bnahill/wireless_logger/sw_imu/src/platform/sf/platform.cpp

/*!
 @file platform.cpp
 
 @brief Platform-specific instantiations
 
 @author Ben Nahill <bnahill@gmail.com>
 */
#define __PLATFORM_CPP_

#include "platform.h"
#include "platform_usbserial.h"
#include "flogfs.h"

#include "imu/ssd1306.cpp"
#include "imu/datasource.cpp"
#include "imu/mma845x.cpp"
#include "imu/clock_mgr.h"


using namespace Platform;

template <GPIO_TypeDef * gpio_temp,
          uint32_t mask,
          uint32_t direction,
          uint32_t pull,
          uint32_t af>
class pin_t {
	static constexpr GPIO_TypeDef * gpio = gpio_temp;
};


I2C Platform::i2c1(I2CD1, OPMODE_I2C, FAST_DUTY_CYCLE_2, 400000, {GPIOB, 9}, {GPIOB, 8});
//I2C Platform::i2c2(I2CD2, OPMODE_I2C, FAST_DUTY_CYCLE_2, 400000, {GPIOH, 5}, {GPIOH, 4});
//I2C Platform::i2c3(I2CD3, OPMODE_I2C, FAST_DUTY_CYCLE_2, 400000, {GPIOC, 9}, {GPIOA, 8});
template class MMA845x<MMA8451Q_T>;
MMA8451Q Platform::acc1(Platform::i2c1, 0x1C);
MAG3110 Platform::mag1(Platform::i2c1, 0x0E);
LPS331 Platform::prs1(Platform::spi3, {NULL, GPIOD, 5, SPI_CR1_BR_2 |
                                       SPI_CR1_BR_1 | SPI_CR1_CPOL |
                                       SPI_CR1_CPHA});


template class DataSource<Euclidean3_f32>;
template class DataListener<Euclidean3_f32>;
DataSource<Euclidean3_f32> Platform::acc_source;
DataSource<Euclidean3_f32> Platform::mag_source;
DataSource<Euclidean3_f32> Platform::gyro_source;

template class DataSource<float>;
template class DataListener<float>;
DataSource<float> Platform::prs_source;

///////////////////////////////////////////
// SPI Platform
///////////////////////////////////////////

SPI Platform::spi1(SPID1);
SPI Platform::spi2(SPID2);
SPI Platform::spi3(SPID3);

///////////////////////////////////////////
// L3GD20 Platform
///////////////////////////////////////////

L3GD20_SPI Platform::gyro1(Platform::spi3, {NULL, GPIOB, 5, SPI_CR1_BR_2 |
                                            SPI_CR1_BR_1 | SPI_CR1_CPOL |
                                            SPI_CR1_CPHA});


///////////////////////////////////////////
// Button platform configuration
///////////////////////////////////////////

button_t Platform::button[4] = {
	{GPIOD, 7, button_t::ACTIVE_LOW},
	{GPIOF, 6, button_t::ACTIVE_LOW},
	{GPIOC, 5, button_t::ACTIVE_LOW},
	{GPIOE, 8, button_t::ACTIVE_LOW}
};

///////////////////////////////////////////
// Edge-trigger interrupt configuration
///////////////////////////////////////////

const EXTConfig Platform::extcfg = {
	{
		{EXT_CH_MODE_DISABLED, NULL}, // 0
		{EXT_CH_MODE_DISABLED, NULL},
		{EXT_CH_MODE_DISABLED, NULL},
		{EXT_CH_MODE_DISABLED, NULL},
		{EXT_CH_MODE_DISABLED, NULL},
		{EXT_CH_MODE_BOTH_EDGES | EXT_CH_MODE_AUTOSTART | EXT_MODE_GPIOC,
			Ext1Callback::callback}, // 5
		{EXT_CH_MODE_BOTH_EDGES | EXT_CH_MODE_AUTOSTART | EXT_MODE_GPIOF,
			Ext1Callback::callback},
		{EXT_CH_MODE_BOTH_EDGES | EXT_CH_MODE_AUTOSTART | EXT_MODE_GPIOD,
			Ext1Callback::callback},
		{EXT_CH_MODE_BOTH_EDGES | EXT_CH_MODE_AUTOSTART | EXT_MODE_GPIOE,
			Ext1Callback::callback},
		{EXT_CH_MODE_DISABLED, NULL},
		{EXT_CH_MODE_DISABLED, NULL}, // 10
		{EXT_CH_MODE_DISABLED, NULL},
		{EXT_CH_MODE_DISABLED, NULL},
		{EXT_CH_MODE_DISABLED, NULL},
		{EXT_CH_MODE_DISABLED, NULL},
		{EXT_CH_MODE_DISABLED, NULL}, // 15
		{EXT_CH_MODE_DISABLED, NULL},
		{EXT_CH_MODE_DISABLED, NULL},
		{EXT_CH_MODE_DISABLED, NULL},
		{EXT_CH_MODE_DISABLED, NULL},
		{EXT_CH_MODE_DISABLED, NULL}, // 20
		{EXT_CH_MODE_DISABLED, NULL},
		{EXT_CH_MODE_DISABLED, NULL}
	}
};

///////////////////////////////////////////
// LED platform configuration
///////////////////////////////////////////

gpio_pin_t Platform::led1(GPIOE, 5);
gpio_pin_t Platform::led2(GPIOE, 3);
gpio_pin_t Platform::led3(GPIOE, 2);


//LTC3559 Platform::reg1({GPIOC, 2}, {GPIOC, 1}, {GPIOA, 4}, {GPIOA, 1});

///////////////////////////////////////////
// OLED display platform configuration
///////////////////////////////////////////


template class SSD1306<4,128>;
template class FrameBuffer<4, 128>;


LY091WG15 Platform::oled(spi1,
                        {NULL, GPIOF, 10, SPI_CR1_BR_0 |
                         SPI_CR1_CPOL | SPI_CR1_CPHA},
                        {GPIOA, 3}, {GPIOH, 2});

usbserial1_t Platform::usbserial1({GPIOA, 9});


///////////////////////////////////////////
// CC1101 platform configuration
///////////////////////////////////////////

// CC1101 Platform::rf1(Platform::spi1,
//                      {NULL, GPIOC, 9, SPI_CR1_BR_2 | SPI_CR1_BR_1});

CC1101 Platform::rf1(Platform::spi2,
                     {NULL, GPIOE, 15, SPI_CR1_BR_2 | SPI_CR1_BR_1});

GuardianRF Platform::guardian1(rf1);

//////////////////////////////////////////////////////////
// Flash platform configuration
//////////////////////////////////////////////////////////

MT29FxG01 Platform::flash(spi1, MT29FxG01::SIZE_1G,
                         {GPIOD, 6},(SPI_CR1_CPOL | SPI_CR1_CPHA));



//////////////////////////////////////////////////////////
// Platform initialization
//////////////////////////////////////////////////////////

EventLog Platform::evt_log;

void Platform::early_init(){
	clk_mgr_init();
	
// 	reg1.high_power(true);
// 	reg1.buck_mode(LTC3559::MODE_BURST);
	rf1.early_init();


	evt_log.init();


	if(flogfs_init() != FLOG_SUCCESS){
		evt_log.add("FLogFS init\n failed!", EventItem::SEVERITY_ERROR);
	} else {
		if(flogfs_mount() != FLOG_SUCCESS){
			evt_log.add("FLogFS mount\n failed!", EventItem::SEVERITY_ERROR);
		}
	}

	
	extStart(&EXTD1, &extcfg);
}


// Lockable * const Platform::buses[] = {
// 	&i2c1,
// 	&spi1,
// 	&spi2,
// 	nullptr
// };

extern "C" {
void NMIVector(void){while(1);}
void HardFaultVector(void){
	asm volatile ("MRS R0,PSP");
	asm volatile ("LDR R1,[R0,#24]");

	while(1);
}
void MemManageVector(void){while(1);}
void BusFaultVector(void){while(1);}
void UsageFaultVector(void){while(1);}
}
