bnahill/wireless_logger/sw_imu/imu/usbserial.h

/*!
 @file usbserial.h
 @brief Declaration for \ref USBSerial driver
 @author Ben Nahill <bnahill@gmail.com>
 */

#ifndef __IMU_USB_SERIAL_H_
#define __IMU_USB_SERIAL_H_

#include "ch.h"
#include "hal.h"
#include "serial_usb.h"
#include "chprintf.h"
#include "imu.h"

//! @addtogroup IMU
//! @{
//! @addtogroup USBSerial
//! @{


/*!
 @brief An abstracted USB CDC device driver
 @tparam usb_driver The ChibiOS USB driver object to use
 
 @note Some of components are declared as generic templated functions but
 some (descriptor info) has to be specialized in the platform
 */
template <USBDriver &usb_driver>
class USBSerial {
public:
	USBSerial< usb_driver >(gpio_pin_t const &vusb_pin) :
		vusb_pin(vusb_pin)
	{
		sduObjectInit(&driver);
	}
	
	/*!
	 @brief Initialize the hardware
	 */
	void init(){
		clk_mgr_req_hse();
		
		//usbDisconnectBus(conf.usbp);
		//chThdSleepMilliseconds(1000);
		//usbStart(conf.usbp, &usbcfg);
		sduObjectInit(&driver);
		sduStart(&driver, &conf);
		
		usbDisconnectBus(conf.usbp);
		chThdSleepMilliseconds(1000);
		usbStart(conf.usbp, &usbcfg);
	    usbConnectBus(conf.usbp);
	}
	
	void stop(){
		usbStop(conf.usbp);
		sduStop(&driver);
		clk_mgr_noreq_hse();
	}
	
	bool is_connected() const { return vusb_pin.read(); }
	
	BaseSequentialStream * stream()  {
		return reinterpret_cast<BaseSequentialStream *>(&driver);
	}
	
	SerialUSBDriverVMT const * vmt() const {
		return driver.vmt;
	}
	
	void write_byte(uint8_t byte){
		chSequentialStreamPut(stream(), byte);
	}
	
	void write_buffer(uint8_t const * buf, uint32_t len){
		chSequentialStreamWrite(&driver, buf, len);
	}
	
	size_t read(uint8_t *bp, size_t n, systime_t time){
		return chIQReadTimeout(&driver.iqueue, bp, n, time);
	}

protected:
	//! @name Implemtented in driver
	//! @{	
	SerialUSBDriver driver;
	gpio_pin_t const vusb_pin;
	
	USBInEndpointState ep1instate;
	USBOutEndpointState ep1outstate;
	USBInEndpointState ep2instate;
	USBOutEndpointState ep2outstate;
	//! @}
	
	//! @name Implemtented in driver
	//! @{

	static USBDescriptor const * get_descriptor(USBDriver *usbp,
	                                            uint8_t dtype,
	                                            uint8_t dindex,
	                                            uint16_t lang);
	
	static const SerialUSBConfig conf;	
	
	static const USBEndpointConfig ep1config;
	static const USBEndpointConfig ep2config;
	
	static const USBDescriptor vcom_strings[];
	
	static const USBConfig usbcfg;
	
	static void usb_event(USBDriver *usbp, usbevent_t event);
	//! @}
	
	//! @name To implement as template specialization
	//! @{

	//! A reference to this device accessible from static context
	static USBSerial &this_device;
	
	static const uint8_t vcom_device_descriptor_data[18];
	static const USBDescriptor vcom_device_descriptor;
	static const uint8_t vcom_configuration_descriptor_data[];
	static const uint8_t vcom_string0[];
	static const uint8_t vcom_string1[];
	static const uint8_t vcom_string2[];
	static const uint8_t vcom_string3[];
	static const USBDescriptor vcom_configuration_descriptor;
	//! @}
};

#include "imu/usbserial.cpp"

//! @} @}

#endif // __IMU_USB_SERIAL_H_
