bnahill/wireless_logger/sw_imu/imu/spi.h

/*!
 @file spi.h
 @brief Declaration for \ref SPI driver
 @author Ben Nahill <bnahill@gmail.com>
 */

#ifndef __IMU_SPI_H_
#define __IMU_SPI_H_

#include "ch.h"
#include "hal.h"
#include "imu/imu.h"

//! @addtogroup IMU
//! @{
//! @addtogroup SPI
//! @{

//class SPI : public LockableSem {
/*!
 @brief A 4-wire SPI driver
 */
class SPI {
public:
	/*
	typedef struct {
		gpio_pin_t nss;
		uint32_t max_freq;
		uint32_t cr1_flags;
	} slave_config_t;
	*/
	
	typedef SPIConfig slave_config_t;
	
	
	typedef enum {
		OP_READ,     //!< A single-word write followed by an arbitrary length
		             //!< read
		OP_WRITE,    //!< A single-word write followed by an arbitrary length
		             //!< write
		OP_EXCHANGE, //!< A simple exchange of two buffers
		OP_SEND,     //!< Just transmit an arbitrary number of bytes
		OP_WR_SEQ,   //!< Write an arbitrary amount of data, then read an
		             //!< arbitrary amount of data
		OP_WW_SEQ,   //!< Write an arbitrary amount of data, then write
		             //!< another arbitrary amount of data
	} operation_t;
	
	typedef void (*callback)(void *);


	struct xfer_t {
		//! Constructor for synchronous exchange
		xfer_t(slave_config_t const * config, size_t n,
		       void const * tx_buff, void * rx_buff) :
			config(config), n_tx(n),
			tc_callback(nullptr), starting_callback(nullptr),
			operation(OP_EXCHANGE), rx_buff(rx_buff), tx_buff(tx_buff)
		{}
		
		//! Constructor for send
		xfer_t(slave_config_t const * config, size_t n, void const * tx_buff) :
			config(config), n_tx(n),
			tc_callback(nullptr), starting_callback(nullptr),
			operation(OP_SEND), tx_buff(tx_buff)
		{}
		
		//! A more generic constructor
		xfer_t(slave_config_t const * config, size_t n, operation_t op) :
			config(config), n_tx(n), operation(op),
			tc_callback(nullptr), starting_callback(nullptr)
		{}

		//! Slave information
		slave_config_t const * config;
		//! @name Callbacks
		//! @brief Set to 0 to not use
		//! @{
		//! Callback for when the transfer is completely done
		callback tc_callback;
		//! Callback for when the transfer is just about to start
		callback starting_callback;
		void *tc_param;
		void *starting_param;
		//! @}
		//! @name Transfer details
		//! @{
		//! The operation to perform
		operation_t operation;
		//! Number of bytes to send or exchange
		size_t n_tx;
		//! Number of bytes to receive (if not exchanging)
		size_t n_rx;
		//! Buffer to write
		void const * tx_buff;
		//! Buffer to store received information
		void * rx_buff;
		//! Address for read or write transfers
		uint16_t addr;
		//! @}
	};
	
	struct new_xfer_t {
		enum {
			XOP_EXCHANGE, //!< A simple exchange of two buffers
			XOP_SEND,     //!< Just transmit an arbitrary number of bytes
			XOP_RECV,     //!< Just receive an arbitrary number of bytes
		} op;
		uint8_t * rx_buff;
		uint8_t const * tx_buff;
		uint32_t n;
		union {
			uint32_t word;
			uint8_t bytes[4];
		};
	};
	
	struct message_t {
		uint32_t num_xfers;
		new_xfer_t * xfer;
		callback tc_callback;
		void *tc_param;
	};
	
	SPI(SPIDriver &driver);
	
	void init();
	
	/*!
	 @brief Add a transfer to the transfer queue
	 @param xfer The transfer to add
	 @param important Push to front of queue?
	 */
	void transfer(xfer_t &xfer, bool important=false);
	
	
	void reconfig_clock();
	
	/*!
	 @brief Perform a synchronous exchange with a peripheral
	 @param config The slave configuration to use
	 @param n The number of bytes to exchange
	 @param tx_buff The n-length buffer to transmit
	 @param rx_buff The n-length receive buffer
	 @param important Force to front of queue?
	 */
	void exchange_sync(slave_config_t const &config, size_t n,
	                   void const * tx_buff, void * rx_buff,
	                   bool important=false);
	
	/*!
	 @brief Perform a synchronous transmission
	 @param config The slave configuration to use
	 @param n The number of bytes to send
	 @param tx_buff The n-length buffer to transmit
	 @param important Force to front of queue?
	 */
	void send_sync(slave_config_t const &config, size_t n,
	               void const * tx_buff, bool important=false);
	
	/*!
	 @brief Perform a synchronous transmission
	 @param config The slave configuration to use
	 @param addr The address to write to
	 @param n The number of bytes to send
	 @param tx_buff The n-length buffer to transmit
	 @param important Force to front of queue?
	 @return The value read during address transmission
	 */
	uint16_t write_sync(slave_config_t const &config, uint16_t addr, size_t n,
	                void const * tx_buff, bool important=false);
	
	/*!
	 @brief Perform a synchronous receive operation
	 @param config The slave configuration to use
	 @param addr The address to write to
	 @param n The number of bytes to send
	 @param rx_buff The n-length buffer to receive to
	 @param important Force to front of queue?
	 @return The value read during address transmission
	 */
	uint16_t read_sync(slave_config_t const &config, uint16_t addr, size_t n,
	                void * rx_buff, bool important=false);
	
	void wr_sequence_sync(slave_config_t const &config, uint8_t const * tx,
	                      uint16_t n_tx, uint8_t * rx, uint16_t n_rx,
	                      bool important = false);
	
	void ww_sequence_sync(slave_config_t const &config, uint8_t const * tx0,
	                      uint16_t n_tx0, uint8_t const * tx1, uint16_t n_tx1,
	                      bool important = false);
	
	void lock(){
		spiAcquireBus(&driver);
	}
	
	void unlock(){
		spiReleaseBus(&driver);
	}
	
protected:
	//! The ChibiOS SPI resource
	SPIDriver &driver;
	
	/*!
	 @brief Flag to indicate that it shouldn't be re-initialized.
	 @note This variable should be accessed only under lock.
	 */
	bool is_init;
	
	bool do_sleep;
};


//! @} @}

#endif // __IMU_SPI_H_
