bnahill/wireless_logger/sw_imu/src/platform/flogfs_conf_implement.h

/*
Copyright (c) 2013, Ben Nahill <bnahill@gmail.com>
All rights reserved.

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
1. Redistributions of source code must retain the above copyright notice, this
   list of conditions and the following disclaimer.
2. Redistributions in binary form must reproduce the above copyright notice,
   this list of conditions and the following disclaimer in the documentation
   and/or other materials provided with the distribution.

THIS SOFTWARE IS PROVIDED BY THE COPYRIGHT HOLDERS AND CONTRIBUTORS "AS IS" AND
ANY EXPRESS OR IMPLIED WARRANTIES, INCLUDING, BUT NOT LIMITED TO, THE IMPLIED
WARRANTIES OF MERCHANTABILITY AND FITNESS FOR A PARTICULAR PURPOSE ARE
DISCLAIMED. IN NO EVENT SHALL THE COPYRIGHT OWNER OR CONTRIBUTORS BE LIABLE FOR
ANY DIRECT, INDIRECT, INCIDENTAL, SPECIAL, EXEMPLARY, OR CONSEQUENTIAL DAMAGES
(INCLUDING, BUT NOT LIMITED TO, PROCUREMENT OF SUBSTITUTE GOODS OR SERVICES;
LOSS OF USE, DATA, OR PROFITS; OR BUSINESS INTERRUPTION) HOWEVER CAUSED AND
ON ANY THEORY OF LIABILITY, WHETHER IN CONTRACT, STRICT LIABILITY, OR TORT
(INCLUDING NEGLIGENCE OR OTHERWISE) ARISING IN ANY WAY OUT OF THE USE OF THIS
SOFTWARE, EVEN IF ADVISED OF THE POSSIBILITY OF SUCH DAMAGE.

The views and conclusions contained in the software and documentation are those
of the authors and should not be interpreted as representing official policies,
either expressed or implied, of the FLogFS Project.
*/

/*!
 * @file flogfs_conf.cpp
 * @author Ben Nahill <bnahill@gmail.com>
 * @ingroup FLogFS
 *
 * @brief Platform-specific interface details
 */

#include "flogfs.h"

#include "platform.h"

using namespace Platform;

typedef uint8_t flash_spare_t[59];

typedef Mutex fs_lock_t;


static inline void fs_lock_init(fs_lock_t * lock){
	chMtxInit(lock);
}

static inline void fs_lock(fs_lock_t * lock){
	chMtxLock(lock);
}

static inline void fs_unlock(fs_lock_t * lock){
	chMtxUnlock();
}

static flash_spare_t flog_spare_buffer;
static uint8_t page_open;

static inline flog_result_t flash_init(){
	return FLOG_RESULT(flash.init());
}

static inline void flash_lock(){
	flash.lock();
}

static inline void flash_unlock(){
	flash.unlock();
}

static inline flog_result_t flash_open_page(uint16_t block, uint16_t page){
	// Read flash page to cache
	return FLOG_RESULT(flash.page_open(block, page));
}

static inline flog_result_t flash_open_page_write(uint16_t block, uint16_t page){
	// Read flash page to cache
	return FLOG_RESULT(flash.page_open_write(block, page));
}

static inline flog_result_t flash_erase_block(uint16_t block){
	return FLOG_RESULT(flash.erase_block(block));
}


static inline uint8_t * flash_spare(uint8_t sector){
	return &flog_spare_buffer[sector * 16 + 4];
}

static inline flog_result_t flash_block_is_bad(){
	uint8_t buffer;
	flash.page_read_continued(&buffer, 0x800, 1);
	return FLOG_RESULT(buffer != 0xFF);
}

static inline void flash_set_bad_block(){

}

/*!
 @brief Commit the changes to the active page
 */
static inline void flash_commit(){
	page_open = 0;
	flash.page_commit();
}

/*!
 @brief Read data from the flash cache (current page only)
 @param dst The destination buffer to fill
 @param chunk_in_page The chunk index within the current page
 @param offset The offset data to retrieve
 @param n The number of bytes to transfer
 @return The success or failure of the operation
 */
static inline flog_result_t flash_read_sector(uint8_t * dst, uint8_t sector, uint16_t offset, uint16_t n){
	sector = sector % FS_SECTORS_PER_PAGE;
	return FLOG_RESULT(flash.page_read_continued(dst, FS_SECTOR_SIZE * sector + offset, n));
}

static inline flog_result_t flash_read_spare(uint8_t * dst, uint8_t sector){
	sector = sector % FS_SECTORS_PER_PAGE;
	return FLOG_RESULT(
	   flash.page_read_continued(dst, 0x804 + sector * 0x10, 4)
	);
}

/*!
 @brief Write chunk data to the flash cache
 @param src A pointer to the data to transfer
 @param chunk_in_page The chunk index within the current page
 @param offset The offset to write the data
 @param n The number of bytes to write
 */
static inline void flash_write_sector(uint8_t const * src, uint8_t sector, uint16_t offset, uint16_t n){
	sector = sector % FS_SECTORS_PER_PAGE;
	flash.page_write_continued(src, FS_SECTOR_SIZE * sector + offset, n);
}


/*!
 @brief Write the spare data for a sector
 @param chunk_in_page The chunk index within the current page

 @note This doesn't commit the transaction
 */
static inline void flash_write_spare(uint8_t const * src, uint8_t sector){
	sector = sector % FS_SECTORS_PER_PAGE;
	flash.page_write_continued(src, 0x804 + sector * 0x10, 4);
}

static inline void flash_debug_warn(char const * msg){
	evt_log.add(msg, EventItem::SEVERITY_WARNING);
}

static inline void flash_debug_error(char const * msg){
	evt_log.add(msg, EventItem::SEVERITY_ERROR);
}
