bnahill/wireless_logger/sw_imu/imu/framebuffer.cpp

/*!
 @file framebuffer.cpp
 
 @brief Templated body for \ref FrameBuffer class
 
 @note This file is not compiled directly; It should be included by your
 platform.
 
 @author Ben Nahill <bnahill@gmail.com>
 */

#include "imu/framebuffer.h"

//! @addtogroup IMU
//! @{
//! @addtogroup FrameBuffer
//! @{

template <uint32_t pages, uint32_t columns>
FrameBuffer< pages, columns >::FrameBuffer(){
	limits.x_min = columns - 1;
	limits.y_min = pages - 1;
	limits.x_max = 0;
	limits.y_max = 0;
	chMtxInit(&mutex);
}

template <uint32_t pages, uint32_t columns>
void FrameBuffer< pages, columns >::clear_area(
	  uint32_t start_page, uint32_t end_page,
	  uint32_t start_column, uint32_t end_column){
	uint32_t i, j;
	lock();
	for(i = start_page; i <= end_page; i++){
		for(j = start_column; j <= end_column; j++){
			fb[i][j] = 0;
		}
	}
	limits.y_min = min(start_page, limits.y_min);
	limits.y_max = max(end_page, limits.y_max);
	limits.x_min = start_column;
	limits.x_max = end_column;
	
	unlock();
}

template <uint32_t pages, uint32_t columns>
void FrameBuffer< pages, columns >::clear(){
	clear_area();
}


template <uint32_t pages, uint32_t columns>
uint32_t FrameBuffer< pages, columns >::write_text_generic(
      write_text_func_t f, char const * text, uint8_t page,
	  uint8_t column, uint32_t max_end_column){
	uint32_t i = 0;
	uint32_t n_cols = 0;
	
	if(*text == 0)
		return n_cols;
	
	lock();
	
	limits.y_min = min(page, limits.y_min);
	limits.x_min = min(column, limits.x_min);
	while(page < pages){
		// Take take the i-th row of the printed text
		if(!f(fb[page] + column, i, text, n_cols,
			                       max_end_column - column)){
			limits.x_max = max(min(n_cols + column, columns), limits.x_max);
			limits.y_max = max(min(page, pages), limits.y_max);
			break;
		}
		
		page += 1;
		i += 1;
	} if (pages == page){
		limits.y_max = pages;
		limits.x_max = max(min(n_cols + column, columns), limits.x_max);
	}
	
	unlock();
	
	return n_cols + column;
}

template <uint32_t pages, uint32_t columns>
void FrameBuffer< pages, columns >::draw_horizontal_mask(uint8_t page,
	  uint8_t mask, uint32_t col_start, uint32_t length){
	uint8_t * iter = &fb[page][col_start];
	lock();
	
	limits.x_min = min(limits.x_min, col_start);
	limits.x_max = max(limits.x_max, col_start + length);
	limits.y_min = min(limits.y_min, page);
	limits.y_max = max(limits.y_max, page);
	while(length--){
		*(iter++) |= mask;
	}
	
	unlock();
}
template <uint32_t pages, uint32_t columns>
void FrameBuffer< pages, columns >::draw_vertical(uint8_t start_page,
	  uint8_t end_page, uint32_t column){
	lock();
	limits.x_min = min(limits.x_min, column);
	limits.x_max = max(limits.x_max, column);
	limits.y_min = min(limits.y_min, start_page);
	limits.x_max = max(limits.y_max, end_page);
	while(start_page != end_page + 1){
		fb[start_page++][column] = 0xFF;
	}
	unlock();
}

template <uint32_t pages, uint32_t columns>
void FrameBuffer< pages, columns >::draw_progress_bar(float value,
	 uint8_t page, uint32_t start_column, uint32_t end_column){

	uint8_t iter;
	uint32_t progress;
	
	value = clamp(value, 0.0f, 1.0f);
	
	progress = value * (end_column - start_column) + 0.5; 
	
	lock();
	limits.x_min = min(limits.x_min, start_column);
	limits.x_max = max(limits.x_max, end_column);
	limits.y_min = min(limits.y_min, page);
	limits.x_max = max(limits.y_max, page);
	
	fb[page][start_column] = 0xFF;
	fb[page][end_column] = 0xFF;
	
	fb[page][start_column + 1] = 0x81;
	for(iter = start_column + 2; iter < progress; iter++){
		fb[page][iter] = 0b10111101; // 0xAD
	}
	for(iter = progress; iter < end_column - 2; iter++){
		fb[page][iter] = 0b10000001; // 0x81
	}
	
	unlock();
}

template <uint32_t pages, uint32_t columns>
void FrameBuffer< pages, columns >::draw_pos_neg_bar(float value,
	  uint8_t page, uint32_t start_column, uint32_t end_column){
	uint8_t iter;
	uint32_t progress;
	uint32_t length = end_column - start_column - 4;
	uint32_t zero_column = start_column + 2 + length / 2;
	
	value = clamp(value, -1.0f, 1.0f);
	
	progress = (int32_t)(0.5f * value * length + 0.5) + zero_column;
	
	lock();
	limits.x_min = min(limits.x_min, start_column);
	limits.x_max = max(limits.x_max, end_column);
	limits.y_min = min(limits.y_min, page);
	limits.x_max = max(limits.y_max, page);
	
	fb[page][start_column] = 0xFF;
	fb[page][end_column] = 0xFF;
	
	// Check if progress bar is to left of zero	
	if(progress < zero_column){
		for(iter = start_column + 1; iter < progress; iter++){
			fb[page][iter] = 0b10000001; // 0x81
		}
		for(iter = progress; iter <= zero_column; iter++){
			fb[page][iter] = 0b10111101; // 0xAD
		}
		for(iter = zero_column + 1; iter < end_column; iter++){
			fb[page][iter] = 0b10000001; // 0x81
		}
	} else {
		for(iter = start_column + 1; iter < zero_column; iter++){
			fb[page][iter] = 0b10000001; // 0x81
		}
		for(iter = zero_column; iter <= progress; iter++){
			fb[page][iter] = 0b10111101; // 0xAD
		}
		for(iter = progress + 1; iter < end_column; iter++){
			fb[page][iter] = 0b10000001; // 0x81
		}
	}
	
	unlock();
}

/*!
	@brief Reset bounds of area to update
	*/
template <uint32_t pages, uint32_t columns>
void FrameBuffer< pages, columns >::sync(bool do_lock){
	if(do_lock)
		lock();
	
	limits.x_min = columns - 1;
	limits.y_min = pages - 1;
	limits.x_max = 0;
	limits.y_max = 0;
	
	if(do_lock)
		unlock();
}

//! @} @}
