bnahill/wireless_logger/sw_imu/src/ui/tests.cpp

#include "tests.h"
#include "platform.h"
#include "ui/ui.h"
#include "stdlib.h"
#include "string.h"
#include "coffee/cfs-coffee.h"
#include "flogfs.h"
#include "acquisition.h"

using namespace Platform;

static void flash_led(){
	led1.set();
	chThdSleep(1);
	led1.clear();
}

bool Tests::flash_power_test(){
	uint8_t test_data[128];
	union {
		flog_write_file_t write_file;
		flog_read_file_t read_file;
	};

	// Each test must disable the OLED, wait 5 ticks, flash the LED, perform the
	// operation, flash the LED, wait 5 more ticks, re-enable the OLED, and
	// then declare the test completed.

	clk_mgr_req_hsi();
	UI::inhibit_suspend();

	flash.init();

	oled.fb.clear_area(1);
	oled.fb.write_text_centered<SmallFont>("First\nErasing a block", 1);
	oled.update();
	UI::wait_for_button(UI::MASK_SELECT);
	oled.sleep();
	chThdSleep(5);
	flash_led();

	flash.erase_block(flash.num_blocks - 1);

	flash_led();
	chThdSleep(5);
	oled.resume();
	oled.fb.clear_area(1);
	oled.fb.write_text_centered<SmallFont>("Done!", 1);
	oled.update();

	UI::wait_for_button(UI::MASK_SELECT);

	oled.fb.clear_area(1);
	oled.fb.write_text_centered<SmallFont>("Now writing\n 1 byte", 1);
	oled.update();
	UI::wait_for_button(UI::MASK_SELECT);
	oled.sleep();
	chThdSleep(5);
	flash_led();

	flash.page_open_write(flash.num_blocks - 1, 0);
	flash.page_write_continued(test_data, 0, 1);
	flash.page_commit();

	flash_led();
	chThdSleep(5);
	oled.resume();
	oled.fb.clear_area(1);
	oled.fb.write_text_centered<SmallFont>("Done!", 1);
	oled.update();




	oled.fb.clear_area(1);
	oled.fb.write_text_centered<SmallFont>("Now writing\n100 bytes", 1);
	oled.update();
	UI::wait_for_button(UI::MASK_SELECT);
	oled.sleep();
	chThdSleep(5);
	flash_led();

	flash.page_open_write(flash.num_blocks - 1, 1);
	flash.page_write_continued(test_data, 0, 100);
	flash.page_commit();

	flash_led();
	chThdSleep(5);
	oled.resume();
	oled.fb.clear_area(1);
	oled.fb.write_text_centered<SmallFont>("Done!", 1);
	oled.update();



	oled.fb.clear_area(1);
	oled.fb.write_text_centered<SmallFont>("Now reading\n1 byte", 1);
	oled.update();
	UI::wait_for_button(UI::MASK_SELECT);
	oled.sleep();
	chThdSleep(5);
	flash_led();

	flash.page_open(flash.num_blocks - 1, 1);
	flash.page_read_continued(test_data, 0, 1);

	flash_led();
	chThdSleep(5);
	oled.resume();
	oled.fb.clear_area(1);
	oled.fb.write_text_centered<SmallFont>("Done!", 1);
	oled.update();



	oled.fb.clear_area(1);
	oled.fb.write_text_centered<SmallFont>("Now reading\n100 bytes", 1);
	oled.update();
	UI::wait_for_button(UI::MASK_SELECT);
	oled.sleep();
	chThdSleep(5);
	flash_led();

	flash.page_open(flash.num_blocks - 1, 1);
	flash.page_read_continued(test_data, 0, 100);

	flash_led();
	chThdSleep(5);
	oled.resume();
	oled.fb.clear_area(1);
	oled.fb.write_text_centered<SmallFont>("Done!", 1);
	oled.update();

	clk_mgr_noreq_hsi();
	UI::enable_suspend();

	return true;
}


bool Tests::fs_power_test() {
	uint8_t test_data[512];
	union {
		flog_write_file_t write_file;
		flog_read_file_t read_file;
	};

	// Each test must disable the OLED, wait 5 ticks, flash the LED, perform the
	// operation, flash the LED, wait 5 more ticks, re-enable the OLED, and
	// then declare the test completed.

	clk_mgr_req_hsi();
	UI::inhibit_suspend();

	flash.init();

	oled.fb.clear_area(1);
	oled.fb.write_text_centered<SmallFont>("First\nFormatting", 1);
	oled.update();
	UI::wait_for_button(UI::MASK_SELECT);
	oled.sleep();
	chThdSleep(5);
	flash_led();

	flogfs_format();
	flogfs_mount();

	flash_led();
	chThdSleep(5);
	oled.resume();
	oled.fb.clear_area(1);
	oled.fb.write_text_centered<SmallFont>("Done!", 1);
	oled.update();

	UI::wait_for_button(UI::MASK_SELECT);

	oled.fb.clear_area(1);
	oled.fb.write_text_centered<SmallFont>("Now opening", 1);
	oled.update();
	UI::wait_for_button(UI::MASK_SELECT);
	oled.sleep();
	chThdSleep(5);
	flash_led();

	flogfs_open_write(&write_file, "testfile");

	flash_led();
	chThdSleep(5);
	oled.resume();
	oled.fb.clear_area(1);
	oled.fb.write_text_centered<SmallFont>("Done!", 1);
	oled.update();

	UI::wait_for_button(UI::MASK_SELECT);

	oled.fb.clear_area(1);
	oled.fb.write_text_centered<SmallFont>("Now writing\n512x10 bytes", 1);
	oled.update();
	UI::wait_for_button(UI::MASK_SELECT);
	oled.sleep();
	chThdSleep(5);
	flash_led();

	for(uint32_t i = 0; i < 10; i++){
		flogfs_write(&write_file, test_data, sizeof(test_data));
	}

	flash_led();
	chThdSleep(5);
	oled.resume();
	oled.fb.clear_area(1);
	oled.fb.write_text_centered<SmallFont>("Done!", 1);
	oled.update();

	flogfs_close_write(&write_file);
	flogfs_open_read(&read_file, "testfile");

	oled.fb.clear_area(1);
	oled.fb.write_text_centered<SmallFont>("Now reading\n512x10 bytes", 1);
	oled.update();
	UI::wait_for_button(UI::MASK_SELECT);
	oled.sleep();
	chThdSleep(5);
	flash_led();

	for(uint32_t i = 0; i < 10; i++){
		flogfs_read(&read_file, test_data, 512);
	}

	flash_led();
	chThdSleep(5);
	oled.resume();
	oled.fb.clear_area(1);
	oled.fb.write_text_centered<SmallFont>("Done!", 1);
	oled.update();


	flogfs_close_read(&read_file);

	UI::wait_for_button(UI::MASK_SELECT);


	clk_mgr_noreq_hsi();
	UI::enable_suspend();

	return true;
}


bool Tests::logging_test(){
	flog_write_file_t f;
	char txt[32];
	constexpr uint32_t buffer_size = 5;
	DataListener<Euclidean3_f32> acc_listener, mag_listener, gyro_listener;
	Euclidean3_f32 acc_buffer[buffer_size], mag_buffer[buffer_size], gyro_buffer[buffer_size];
	
	Euclidean3_f32 reading;
	Euclidean3_f32 *reading_ptr;
	
	acc_listener.init(acc_buffer, buffer_size);
	mag_listener.init(mag_buffer, buffer_size);
	gyro_listener.init(gyro_buffer, buffer_size);
	
	flogfs_mount();
	flogfs_open_write(&f, "logger");
	
	acc_source.register_queue(acc_listener);
	mag_source.register_queue(mag_listener);
	gyro_source.register_queue(gyro_listener);
	
	Acquisition::require_sources(Acquisition::SRC_ACC1);
	Acquisition::require_sources(Acquisition::SRC_MAG1);
	Acquisition::require_sources(Acquisition::SRC_GYRO1);
	
	oled.fb.clear_area(1);
	oled.fb.write_text_centered<SmallFont>("Writing...", 2);
	oled.update();

	UI::handle_evt(UI::MASK_SUSPEND);
	
	// Take 6000 readings (one minute at 100Hz)
	for(uint32_t i = 0; i < 6000;){
		if(acc_listener.receive_to(reading, TIME_IMMEDIATE)){
			flogfs_write(&f, (uint8_t const *)&reading, sizeof(reading));
			i += 1;
			//imu_sprint(txt, "Sample ", i);
			//oled.fb.write_text_centered<SmallFont>(txt, 3);
			//oled.update();
		}
		if(mag_listener.receive_to(reading, TIME_IMMEDIATE)){
			flogfs_write(&f, (uint8_t const *)&reading, sizeof(reading));
		}
		if(gyro_listener.receive_to(reading, TIME_IMMEDIATE)){
			flogfs_write(&f, (uint8_t const *)&reading, sizeof(reading));
		}
	}
	
	UI::handle_evt(UI::MASK_RESUME);
	
	Acquisition::norequire_sources(Acquisition::SRC_ACC1);
	Acquisition::norequire_sources(Acquisition::SRC_MAG1);
	Acquisition::norequire_sources(Acquisition::SRC_GYRO1);
	
	oled.fb.clear_area(1);
	oled.fb.write_text_centered<SmallFont>("Done!", 2);
	
	flogfs_close_write(&f);
	
	UI::wait_for_button(UI::MASK_SELECT);
	
	return true;
}

bool Tests::fs_test() {
	bool res;
	uint8_t buffer[1024];
	flog_write_file_t write_file;
	flog_read_file_t read_file;
	char txt[32];
	uint32_t t0, t1;
	

	for(uint32_t i = 0; i < 1024; i++){
		buffer[i] = i * 5;
	}

	txt[0] = 0;

	oled.fb.clear_area(1);
	oled.fb.write_text_centered<SmallFont>("Press SELECT\nto Advance", 2);
	oled.update();

	UI::wait_for_button(UI::MASK_SELECT);
	
	//goto mount;

	oled.fb.clear_area(1);
	oled.fb.write_text_centered<SmallFont>("Formatting...", 2);
	oled.update();
	led1.set();
	res = (flogfs_format() == FLOG_SUCCESS);
	led1.clear();
	if(!res) goto failure;
	oled.fb.write_text_centered<SmallFont>("Success", 3);
	oled.update();

	UI::wait_for_button(UI::MASK_SELECT);

mount:

	// Mount it
	oled.fb.clear_area(1);
	oled.fb.write_text_centered<SmallFont>("Mounting...", 2);
	oled.update();
	led1.set();
	res = (flogfs_mount() == FLOG_SUCCESS);
	led1.clear();
	if(!res) goto failure;
	oled.fb.write_text_centered<SmallFont>("Success", 3);
	oled.update();

	UI::wait_for_button(UI::MASK_SELECT);
	
	//goto erase_test;

	oled.fb.clear_area(1);
	oled.fb.write_text_centered<SmallFont>("Making big file", 2);
	oled.update();
	led1.set();
	res = (flogfs_open_write(&write_file, "test") == FLOG_SUCCESS);
	led1.clear();
	if(!res){
		imu_sprint(txt, "Failed opening");
		goto failure;
	}
	
	oled.fb.write_text_centered<SmallFont>("Success", 3);
	oled.update();
	
	UI::wait_for_button(UI::MASK_SELECT);

	oled.fb.clear_area(1);
	oled.fb.write_text_centered<SmallFont>("Writing big file", 2);
	oled.update();
	led1.set();
	t0 = chTimeNow();
	for(uint32_t i = 0; i < 1024*5; i++){
		uint32_t count = flogfs_write(&write_file, buffer, sizeof(buffer));
		if((i & 0x1F) == 0){
		//	imu_sprint(txt, "Wrote ", write_file.write_head / 1024, " kB");
		//	oled.fb.write_text_centered<SmallFont>(txt, 3);
			// oled.update();
		}
		if(count != sizeof(buffer)){
			// Disk presumably full!
			break;
		}
	}
	t1 = chTimeNow();
	led1.clear();
	oled.fb.clear_area(1);
	imu_sprint(txt, "Wrote ", write_file.write_head / 1024, " kB\nin ", (uint32_t)(1000*(t1-t0))/MS2ST(1000), " ms");
	oled.fb.write_text_centered<SmallFont>(txt, 2);
	oled.update();
	txt[0] = 0;

	UI::wait_for_button(UI::MASK_SELECT);

	oled.fb.clear_area(1);
	oled.fb.write_text_centered<SmallFont>("Closing file", 2);
	oled.update();
	// Don't care about return, it should fail since it can't finish allocation
	flogfs_close_write(&write_file);
	oled.fb.write_text_centered<SmallFont>("Success", 3);
	oled.update();
	
	UI::wait_for_button(UI::MASK_SELECT);
	
read_test:
	
	oled.fb.clear_area(1);
	oled.fb.write_text_centered<SmallFont>("Opening file", 2);
	oled.update();
	led1.set();
	res = (flogfs_open_read(&read_file, "test") == FLOG_SUCCESS);
	led1.clear();
	if(!res){
		imu_sprint(txt, "Failed opening");
		goto failure;
	}
	oled.fb.write_text_centered<SmallFont>("Done!", 3);
	oled.update();
	UI::wait_for_button(UI::MASK_SELECT);
	oled.fb.clear_area(1);
	oled.fb.write_text_centered<SmallFont>("Reading File", 2);
	oled.update();
	t0 = chTimeNow();
	while(flogfs_read(&read_file, buffer, 1024) == 1024);
	t1 = chTimeNow();
	
	flogfs_close_read(&read_file);
	
	imu_sprint(txt, "Read ", read_file.read_head / 1024, " kB\nin ", (uint32_t)(1000*(t1-t0))/MS2ST(1000), " ms");
	oled.fb.write_text_centered<SmallFont>(txt, 2);
	oled.update();
	txt[0] = 0;
	
	UI::wait_for_button(UI::MASK_SELECT);
	
erase_test:
	
	oled.fb.clear_area(1);
	oled.fb.write_text_centered<SmallFont>("Erasing File", 2);
	oled.update();
	led1.set();
	t0 = chTimeNow();
	flogfs_rm("test");
	t1 = chTimeNow();
	led1.clear();
	imu_sprint(txt, "Deleted in ", (uint32_t)(1000*(t1-t0))/MS2ST(1000), " ms");
	oled.fb.write_text_centered<SmallFont>(txt, 2);
	oled.update();
	txt[0] = 0;
	
	UI::wait_for_button(UI::MASK_SELECT);

	oled.fb.clear_area(1);
	oled.fb.write_text_centered<SmallFont>("Done!", 2);
	oled.update();

	// All tests passed!

	UI::wait_for_button(UI::MASK_SELECT);
	return true;

failure:
	if(txt[0] == 0)
		imu_sprint(txt, "Failure");
	oled.fb.write_text_centered<SmallFont>(txt, 3);
	oled.update();
	UI::wait_for_button(UI::MASK_SELECT);
	return false;
}

bool Tests::fs_format() {
	bool res;
	oled.fb.clear_area(1);

	oled.fb.write_text_centered<SmallFont>("Formatting...", 2);
	oled.update();
	res = (flogfs_format() == FLOG_SUCCESS);

	oled.fb.clear_area(1);
	if(res){
		oled.fb.write_text_centered<SmallFont>("Success", 2);
	} else {
		oled.fb.write_text_centered<SmallFont>("Failed", 2);
	}
	oled.update();
	UI::wait_for_button(UI::MASK_SELECT);
	return res;
}


bool Tests::fs_mount(){
	bool res;
	oled.fb.clear_area(1);

	oled.fb.write_text_centered<SmallFont>("Mounting...", 2);
	oled.update();
	res = (flogfs_mount() == FLOG_SUCCESS);

	oled.fb.clear_area(1);
	if(res){
		oled.fb.write_text_centered<SmallFont>("Success", 2);
	} else {
		oled.fb.write_text_centered<SmallFont>("Failed", 2);
	}
	oled.update();
	UI::wait_for_button(UI::MASK_SELECT);
	return res;
}

bool Tests::flash_erase(){
	oled.fb.clear_area(1);

	oled.fb.write_text_centered<SmallFont>("Erasing...", 2);
	for(auto i = flash.num_blocks - 1; i; i--){
		flash.erase_block(i);
	}
	oled.fb.clear_area(1);
	oled.fb.write_text_centered<SmallFont>("Done", 2);
	UI::wait_for_button(UI::MASK_SELECT);
	return true;
}

bool Tests::flash_ecc_flexibility_test() {
	uint32_t constexpr block = 11;
	uint32_t constexpr page = 0;
	uint32_t constexpr bytes = 2112;
	
	char textbuffer[32];
	
	uint8_t buffer[bytes];
	
	oled.fb.clear_area(1);

	oled.fb.write_text_centered<SmallFont>("Starting", 2);
	oled.update();

	textbuffer[0] = 0;
	
	for(uint32_t i = 0; i < bytes; i++){
		buffer[i] = i;
	}
	
	flash.lock();
	flash.erase_block(block);
	
	// Write to protected areas
	
	flash.page_open(block, page);
	flash.page_write_continued(buffer, 0, 512);
	flash.page_write_continued(buffer, 0x804, 4);
	flash.page_commit();
	
	flash.page_open(block, page);
	flash.page_write_continued(buffer + 0x200, 0x200, 512);
	flash.page_write_continued(buffer, 0x814, 4);
	flash.page_commit();
	
	flash.page_open(block, page);
	flash.page_write_continued(buffer + 0x400, 0x400, 512);
	flash.page_write_continued(buffer, 0x824, 4);
	flash.page_commit();
	
	flash.page_open(block, page);
	flash.page_write_continued(buffer + 0x600, 0x600, 512);
	flash.page_write_continued(buffer, 0x834, 4);
	flash.page_commit();
	
	// Write to unprotected areas
	
	flash.page_open(block, page);
	flash.page_write_continued(buffer, 0x802, 2);
	flash.page_commit();
	
	flash.page_open(block, page);
	flash.page_write_continued(buffer, 0x812, 2);
	flash.page_commit();
	
	flash.page_open(block, page);
	flash.page_write_continued(buffer, 0x822, 2);
	flash.page_commit();
	
	flash.page_open(block, page);
	flash.page_write_continued(buffer, 0x832, 2);
	flash.page_commit();
	
	flash.unlock();
	
	// Check protected areas
	
	if(!flash.read_page(buffer, block, page, 0, 2048)){
		imu_sprint(textbuffer, "Failed to read\nmain!");
		goto end;
	}
	
	if(!flash.read_page(buffer, block, page, 0, 2048)){
		imu_sprint(textbuffer, "Failed to read\nmain twice!");
		goto end;
	}
	
	
	
	for(uint32_t i = 0; i < 2048; i++){
		if(buffer[i] != static_cast<uint8_t>(i)){
			imu_sprint(textbuffer, "Error at ", i);
			goto end;
		}
	}
	
	if(!flash.read_page(buffer, block, page, 0x802, 2)){
		imu_sprint(textbuffer, "Failed to read\nspare 0!");
		goto end;
	}
	
	for(uint32_t i = 0; i < 2; i++){
		if(buffer[i] != static_cast<uint8_t>(i)){
			imu_sprint(textbuffer, "Error spare 0\nat ", i);
			goto end;
		}
	}
	
	if(!flash.read_page(buffer, block, page, 0x812, 2)){
		imu_sprint(textbuffer, "Failed to read\nspare 1!");
		goto end;
	}
	
	for(uint32_t i = 0; i < 2; i++){
		if(buffer[i] != static_cast<uint8_t>(i)){
			imu_sprint(textbuffer, "Error spare 1\nat ", i);
			goto end;
		}
	}
	
	if(!flash.read_page(buffer, block, page, 0x822, 2)){
		imu_sprint(textbuffer, "Failed to read\nspare 2!");
		goto end;
	}
	
	for(uint32_t i = 0; i < 2; i++){
		if(buffer[i] != static_cast<uint8_t>(i)){
			imu_sprint(textbuffer, "Error spare 2\nat ", i);
			goto end;
		}
	}
	
	if(!flash.read_page(buffer, block, page, 0x832, 2)){
		imu_sprint(textbuffer, "Failed to read\nspare 3!");
		goto end;
	}

	for(uint32_t i = 0; i < 2; i++){
		if(buffer[i] != static_cast<uint8_t>(i)){
			imu_sprint(textbuffer, "Error spare 3\nat ", i);
			goto end;
		}
	}
	
	imu_sprint(textbuffer, "Success!");

end:
	
	
	oled.fb.write_text_centered<SmallFont>(textbuffer, 2);
	
	UI::wait_for_button(UI::MASK_SELECT);
	
	return true;
}




bool Tests::flash_create_test_file(){
	int fd;
	constexpr auto size = 2048;
	char testbuffer[size], readbuffer[size];
	oled.fb.clear_area(1);
	oled.fb.write_text<SmallFont>("Writing...", 1, 0);
	oled.update();
	fd = cfs_open("testfile", CFS_WRITE);
	if(-1 == fd){
		oled.fb.write_text<SmallFont>("Error opening file", 2, 0);
		goto error;
	}
	for(uint32_t i = 0; i < size; i++){
		testbuffer[i] = i & 77;
	}
	if(cfs_write(fd, testbuffer, size) != size){
		oled.fb.write_text<SmallFont>("Error writing file", 2, 0);
		goto error;
	}
	
	cfs_close(fd);
	
	
	
	oled.fb.clear_area(1);
	oled.fb.write_text<SmallFont>("Reading...", 1, 0);
	oled.update();
	fd = cfs_open("testfile", CFS_READ);
	if(-1 == fd){
		oled.fb.write_text<SmallFont>("Error opening file", 2, 0);
		goto error;
	}
	if(cfs_read(fd, readbuffer, size) != size){
		oled.fb.write_text<SmallFont>("Error reading file", 2, 0);
		goto error;
	}
	cfs_close(fd);
	if(memcmp(testbuffer, readbuffer, size) != 0){
		oled.fb.write_text<SmallFont>("RW data doesn't match", 2, 0);
		goto error;
	}
	oled.fb.write_text<SmallFont>("Tests passed!", 2, 0);
	oled.update();
	UI::wait_for_button(UI::MASK_SELECT);
	return true;
error:
	oled.update();
	UI::wait_for_button(UI::MASK_SELECT);
	return false;
}

bool Tests::flash_bad_block_check(){
	uint32_t bad_block_count;
	char text[32] = "Bad blocks:";
	oled.fb.clear_area(1);
	
	oled.fb.write_text<SmallFont>("Checking bad blocks...", 1, 0);
	oled.update();
	
	bad_block_count = 0;
	for(uint16_t i = 0; i < flash.num_blocks; i++){
		if(flash.check_block_bad(i)){
			bad_block_count += 1;
		}
	}
	
	uint_to_string(bad_block_count, text+11);
	oled.fb.write_text<SmallFont>(text, 2, 0);
	oled.update();
	
	UI::wait_for_button(UI::MASK_SELECT);

	return true;
}

bool Tests::flash_test(){
	MT29FxG01::page_t * write_buff;
	MT29FxG01::page_t * read_buff;
	uint32_t i;
	
	constexpr uint16_t block = 44;
	constexpr uint16_t page = 0;
	
	bool err = false;
	
	oled.fb.clear_area(1);
	
	write_buff = reinterpret_cast<MT29FxG01::page_t *>(chPoolAlloc(&flash.pool));
	read_buff = reinterpret_cast<MT29FxG01::page_t *>(chPoolAlloc(&flash.pool));
	
	if(write_buff){
		oled.fb.write_text<SmallFont>("Allocated 1", 1, 0);
	} else {
		oled.fb.write_text<SmallFont>("Didn't allocate", 1, 0);
		err = true;
	}
	
	if(read_buff){
		oled.fb.write_text<SmallFont>("Allocated 2", 2, 0);
	} else {
		oled.fb.write_text<SmallFont>("Didn't allocate", 2, 0);
		err = true;
	}
	
	oled.update();
	
	
	if(err){
		goto dont_run;
	}
	
	
	chThdSleep(MS2ST(2000));
	
	
	oled.fb.clear_area(1);
	oled.fb.write_text<SmallFont>("Erasing block", 1, 0);
	oled.update();
	if(!flash.erase_block(block)){
		oled.fb.write_text<SmallFont>("Failure reported", 2, 0);
		err = true;
	} else {
		oled.fb.write_text<SmallFont>("Success reported", 2, 0);
	}
	oled.update();
	if(err) goto dont_run;
	
	
	chThdSleep(MS2ST(2000));
	Random::init();
	for(i = 0; i < flash.page_size; i++){
		(static_cast<uint8_t *>(*write_buff))[i] = (uint8_t)Random::get_value();
	}
	Random::close();
		
	oled.fb.clear_area(1);
	oled.fb.write_text<SmallFont>("Write random block", 1, 0);
	oled.update();
	if(flash.write_page(*write_buff, block, page)){
		oled.fb.write_text<SmallFont>("Success reported", 2, 0);
	} else {
		oled.fb.write_text<SmallFont>("Failure reported", 2, 0);
		err = true;
	}
	oled.update();
	
	if(err) goto dont_run;
	
	chThdSleep(MS2ST(2000));
	
	oled.fb.clear_area(1);
	oled.fb.write_text<SmallFont>("Read back block", 1, 0);
	oled.update();
	if(flash.read_page(reinterpret_cast<uint8_t *>(*read_buff), block, page, 0, flash.page_size)){
		oled.fb.write_text<SmallFont>("Success reported", 2, 0);
	} else {
		oled.fb.write_text<SmallFont>("Failure reported", 2, 0);
	}
	oled.update();
	
	chThdSleep(MS2ST(2000));
	
	oled.fb.clear_area(1);
	oled.fb.write_text<SmallFont>("Comparing", 1, 0);
	oled.update();
	
	for(i = 0; i < flash.page_size; i++){
		if(reinterpret_cast<uint8_t *>(*write_buff)[i] != reinterpret_cast<uint8_t *>(*read_buff)[i]){
			oled.fb.write_text<SmallFont>("Mismatch found", 2, 0);
			break;
		}
	} if(i == flash.page_size){
		oled.fb.write_text<SmallFont>("Test passed!", 2, 0);
	}
	
	oled.update();
	
	
	chPoolFree(&flash.pool, write_buff);
	chPoolFree(&flash.pool, read_buff);
	
dont_run:

	
	// Wait for select button
	UI::wait_for_button(UI::MASK_SELECT);
	
	return true;
}
